signalkinetics/Underwater-Backscatter/PCB Eagle Schematic/PAB_cricuit_layout.sch

## EAGLE design PCB Eagle Schematic/PAB_cricuit_layout.sch (2020-07-24)

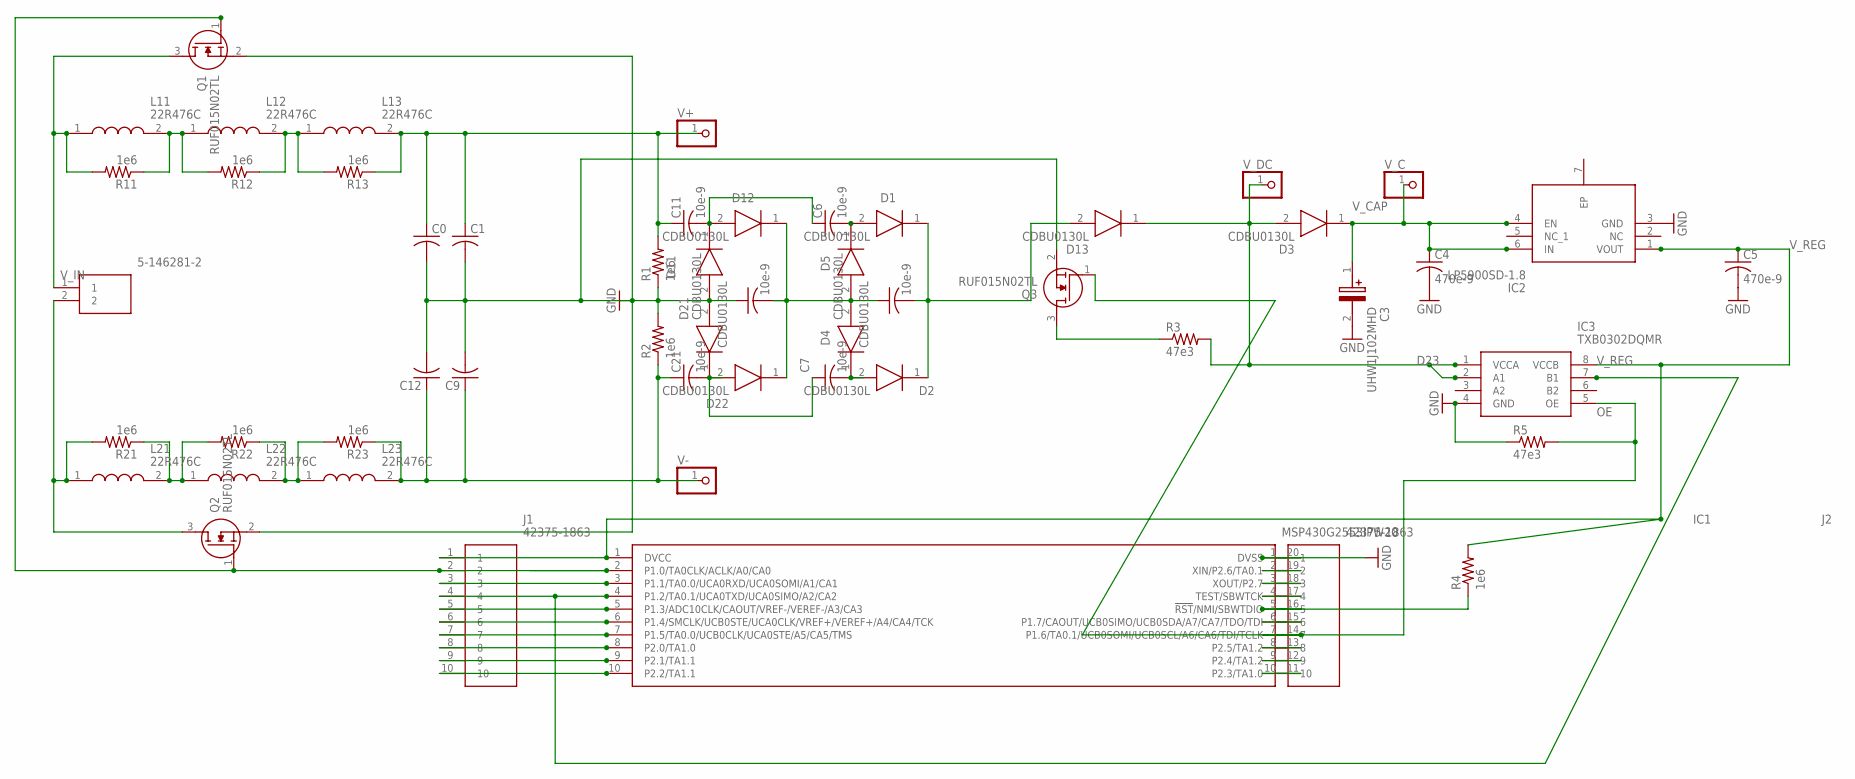
[picture p25: schematic PAB_cricuit_layout.sch]

Parts:
C0, C1, C9, C12: C-USC0603; C0603
C3: UHW1J102MHD; CAPPRD500W80D1250H4200
C4, C5: 470e-9; C0603
C6, C7, C8, C11, C21, C22: 10e-9; C0603
D1, D2, D3, D4, D5, D11, D12, D13, D21, D22: CDBU0130L; DIOM179X85N
IC1: MSP430G2553IPW20; SOP65P640X120-20N
IC2: LP5900SD-1.8; SON65P250X220X80-7N
IC3: TXB0302DQMR; SON40P120X180X40-8N
J1, J2: 42375-1863; HDRV10W87P0X254_1X10_2540X249X
L11, L12, L13, L21, L22, L23: 22R476C; 22R335C
Q1, Q2, Q3: RUF015N02TL; SOT65P210X85-3N
R1, R2, R4, R11, R12, R13, R21, R22, R23: 1e6; R0603
R3, R5: 47e3; R0603
V+: PINHD-1X1; 1X01
V-: PINHD-1X1; 1X01
V_C: PINHD-1X1; 1X01
V_DC: PINHD-1X1; 1X01
V_IN: 5-146281-2; HDRV2W67P0X254_1X2_721X234X821

Connections:
D23: D3.2 (K), D13.1 (A), IC3.1 (VCCA), IC3.2 (A1), R3.2, V_DC.1
GND: C0.2, C1.2, C3.2 (-), C4.2, C5.2, C9.2, C12.2, C22.1, D11.2 (K), D21.2 (K), IC1.20 (DVSS), IC2.3 (GND), IC3.4 (GND), J2.1, Q1.2 (S), Q2.2 (S), Q3.2 (S), R1.1, R2.2, R5.1
J3: C8.1, D4.2 (K), D5.2 (K)
unnamed: C6.1, C11.2, D11.1 (A), D12.2 (K)
unnamed: C22.2, D12.1 (A), D22.1 (A)
unnamed: L11.2, L12.1, R11.1, R12.2
unnamed: L21.2, L22.1, R21.1, R22.2
unnamed: L21.1, Q2.3 (D), R21.2, V_IN.2
unnamed: C7.1, C21.2, D21.1 (A), D22.2 (K)
unnamed: C7.2, D2.2 (K), D4.1 (A)
unnamed: L12.2, L13.1, R12.1, R13.2
unnamed: IC1.4 (P1.2/TA0.1/UCA0TXD/UCA0SIMO/A2/CA2), IC3.7 (B1), J1.4
unnamed: IC1.3 (P1.1/TA0.0/UCA0RXD/UCA0SOMI/A1/CA1), J1.3
unnamed: IC1.5 (P1.3/ADC10CLK/CAOUT/VREF-/VEREF-/A3/CA3), J1.5
unnamed: IC1.6 (P1.4/SMCLK/UCB0STE/UCA0CLK/VREF+/VEREF+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), J1.6
unnamed: L22.2, L23.1, R22.1, R23.2
unnamed: IC1.7 (P1.5/TA0.0/UCB0CLK/UCA0STE/A5/CA5/TMS), J1.7
unnamed: IC1.8 (P2.0/TA1.0), J1.8
unnamed: IC1.9 (P2.1/TA1.1), J1.9
unnamed: IC1.10 (P2.2/TA1.1), J1.10
unnamed: IC1.2 (P1.0/TA0CLK/ACLK/A0/CA0), J1.2, Q1.1 (G), Q2.1 (G)
unnamed: Q3.3 (D), R3.1
unnamed: IC1.19 (XIN/P2.6/TA0.1), J2.2
unnamed: IC1.18 (XOUT/P2.7), J2.3
unnamed: IC1.17 (TEST/SBWTCK), J2.4
unnamed: IC1.16 (!RST!/NMI/SBWTDIO), J2.5, R4.1
unnamed: IC1.15 (P1.7/CAOUT/UCB0SIMO/UCB0SDA/A7/CA7/TDO/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), J2.6
unnamed: C9.1, C12.1, C21.1, L23.2, R2.1, R23.1, V-.1
unnamed: IC1.13 (P2.5/TA1.2), J2.8
unnamed: IC1.12 (P2.4/TA1.2), J2.9
unnamed: IC1.11 (P2.3/TA1.0), J2.10
unnamed: C6.2, D1.2 (K), D5.1 (A)
unnamed: C8.2, D1.1 (A), D2.1 (A), D13.2 (K)
OE: IC1.14 (P1.6/TA0.1/UCB0SOMI/UCB0SCL/A6/CA6/TDI/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), IC3.5 (OE), J2.7, Q3.1 (G), R5.2
V+: C0.1, C1.1, C11.1, L13.2, R1.2, R13.1, V+.1
V_CAP: C3.1 (+), C4.1, D3.1 (A), IC2.4 (EN), IC2.6 (IN), V_C.1
V_IN+: L11.1, Q1.3 (D), R11.2, V_IN.1
V_REG: C5.1, IC1.1 (DVCC), IC2.1 (VOUT), IC3.8 (VCCB), J1.1, R4.2
